stanislawkrowicki/put-ask/hardware/sim/LED_33to5Inv.asc

Q1: npn; 2N3904
R1: res; 10k
R2: res; 1k
V1: voltage; PULSE(0 3.3 0 0.0001 0.0001 0.001 0.002 5)
V2: voltage; 5V
Named nets: 0
.tran 0 0.1 0 1000
